RGuise-Brown/Battery_Management_FYP/firmware/Inc/led.h

/*
 * led.h
 *
 *  Created on: Sep 20, 2025
 *      Author: rachaelguise-brown
 *
 *      Description: to code the blue LED (LED2) to flash
 *      Basic tesing to see the board is working
 */

#ifndef LED_H_
#define LED_H_

void LED2_Config(void);
void LED2_On(void);
void LED2_Off(void);
void LED2_Toggle(void);


#endif /* LED_H_ */
